thecannawiki/ESP32EnvironmentController/src/globals.cpp

#include "Arduino.h"
#include <EEPROM.h>            // read and write from flash memory
#ifdef HTTP_DELETE
#undef HTTP_DELETE
#endif
// #include <ESPAsyncWebServer.h>
#include "esp_task_wdt.h"      //to feed the task watchdog
#include <vector>
#include <algorithm>
#include "Credentials.h"  
#include <WiFi.h>
#include <WiFiMulti.h>
#include <Wire.h>
#include <SPI.h>
#include <PubSubClient.h>
#include <Adafruit_NeoPixel.h>
#include <ArduinoJson.h>
#include <Preferences.h>
#include <buffer.h>
#include <SensirionI2CScd4x.h>
#include <SparkFunBME280.h> //edit this library to change the i2c address if bme is not found
#include <SparkFun_SGP30_Arduino_Library.h>
#include "globals.h"

SensirionI2CScd4x scd4x;
bool SCD40Mounted = false;
BME280 bme280;
SGP30 sgp30;
bool bmeMounted = false;
bool sgpMounted = false;
Sensor sensorPref = SCD4;


//global vals
//hardware
bool dehumidiferState = false;
bool humidifierState = false;
bool automaticDehumidifier = true;
bool automaticHumidifier = true;
bool automaticFanVpd = true;
bool dehumidifierPrimaryMode = false; // Primary mode means dehumidifier/humidifier will operate on bounds around target humidity. When false (secondary mode) it will control based on fan power usage
bool dehumidifierForTemp = false; // The dehumidifier  will operate on bounds around target temperature. This takes precedence over dehumidifier secondary mode when enabled
int heaterMaxPower = 50;
float heaterPower = heaterMaxPower;
float humidifierPower = 0;
bool heaterTempMode = false;
bool autoHeater = false;
bool pumpState = false;
float fanPower = 30.0f;        //float to 1dp between 0 and 100
float lastPowerVal = 0;        //for fan ramp up control
float minpercentvalue = 0.0f; //min power percentage required to make fan spin e.g 0.25 for 25%
float softMaxFan = 100.0f; //soft upper limit on fan percentage
float softMinFan = 0.0f; //soft lower limit on fan percentage
bool lockHVAC = false;
unsigned long pumpEnd = 0;
unsigned long pumpStart = 0;
unsigned long heaterStart = 0;
unsigned long heaterEnd = 0;
float waterSensor1State = 0;
int w2raw = 0;
float w2mean = 0;

//settings
float targetHumidity = 60;  //Sensible default
float targetVpd = 1.0f;
float targetTemperature = 25.0f;
float ventTemp = 35.0f;
int w1maxWaterSensorVal = 1800;
int w2maxWaterSensorVal = 1800;
bool vpdMode = true;
bool setupMode = false;
char deviceName[40] = "";
char MQTTPUBLISHTOPIC[50] = "";
char MQTTCONTROLTOPIC[50] = "";

//pinout
int dehumidifierControlPin = 34;
int touchWaterSensor = 14;
int humidifierControlPin = 13;
int fanControlPin = 12;
int pumpControlPin = 33;
int waterSensor1Pin= 34;
// int waterSensor2Pin= 4;
int heaterControlPin = 27;
int neopixelPin = 19;
int setupModePin = 23;

//environ vals
float temp = -1;
float humidity = -1;

uint16_t co2 = -1;
float tvoc = 0;
float upperHumidityBound = 60.0f;
float lowerHumidityBound = 40.0f;
char sensorjson[SENSORJSON_SIZE];


Buffer<64> humidityBuffer ;  ///written to every SensorTime
Buffer<64> tempBuffer;
Buffer<64> errorBuffer;
Buffer<64> w1Buffer;
Buffer<128> w2Buffer;
Buffer<500> fanBuffer;   //written to every second
Buffer<500> heaterStateBuffer;   //written to every second
Buffer<300> humidifierStateBuffer;   //written to every second


//PID
float P = 0.1;
float I = 0.1;
float D = 0.1;

//heater PID
float HP = 0.1;
float HD = 0.1;
float HVPDP = 1; // heater vpd (PID) P term
float HVPDD = 1; // heater vpd (PID) D term
float HuVPD_P = 1;
float HuVPD_D = 1;




//time
const char* ntpServer = "pool.ntp.org";
long gmtOffset_sec = 0;
int daylightOffset_sec = 3600;
struct tm timeinfo;
time_t timeNow;

//mqtt
long lastMsg = 0;
char msg[50];
int value = 0;

// setting PWM properties
int freq = 200000;
int heaterFreq = 20000;
int humidifierFreq = 20000;
int fanPWMchannel = 0;
int heaterPWMchannel = 1;
int humidifierPWMchannel = 2;
int resolution = 10;    //10-bit
int maxPWMval = 1023;  // for resolution of 10-bit
bool fanChanged = false;
float fanPowerLimiter = 1.0f; //0-1, limits the fan power to a percentage of the maxPWMval
float heaterSoftMaxPWM = (MAXHEATEROUTPUT / 100.0) * maxPWMval;

//global objects
WiFiMulti wifiMulti;
// AsyncWebServer server(80);
Adafruit_NeoPixel pixels(1, neopixelPin, NEO_GRB + NEO_KHZ800);

TaskHandle_t longPWMTaskHandle = NULL;
TaskHandle_t TransTestTaskHandle = NULL;
TaskHandle_t LedAnimationTaskHandle = NULL;
TaskHandle_t freezewatchdogTaskHandle = NULL;
TaskHandle_t mainLoopTaskHandle = NULL;
TaskHandle_t mqttTaskHandle = NULL;
WiFiClientSecure espClient;
PubSubClient mqttclient(espClient);
Preferences preferences;

//runtime 
int loopCounter = 0;
bool setupReceived = false;
int transTestTime = 0;
time_t humidifierPauseTime = 0;
