thecannawiki/ESP32EnvironmentController/src/globals.h

#include "Arduino.h"
#include <EEPROM.h>            // read and write from flash memory
// #include <ESPAsyncWebServer.h>
#include "esp_task_wdt.h"      //to feed the task watchdog
#include <vector>
#include <algorithm>
#include "Credentials.h"  
#include <WiFi.h>
#include <WiFiMulti.h>
#include <Wire.h>
#include <SPI.h>

#include <PubSubClient.h>
#include <WiFiClientSecure.h>
#include <Adafruit_NeoPixel.h>
#include <ArduinoJson.h>
#include <Preferences.h>
#include "buffer.h"
#include <SensirionI2CScd4x.h>
#include <SparkFunBME280.h> //edit this library to change the i2c address if bme is not found
#include <SparkFun_SGP30_Arduino_Library.h>

#ifndef GLOBALS_H
#define GLOBALS_H

enum Sensor {BM280_SGP30, SCD4};

extern SensirionI2CScd4x scd4x;
extern bool SCD40Mounted;
extern BME280 bme280;
extern SGP30 sgp30;
extern bool bmeMounted;
extern bool sgpMounted;
extern Sensor sensorPref;
//global vals
//hardware


extern bool dehumidiferState;
extern bool humidifierState;
extern bool automaticDehumidifier;
extern bool automaticHumidifier;
extern bool automaticFanVpd;
extern bool dehumidifierPrimaryMode;
extern bool dehumidifierForTemp;
extern int heaterMaxPower;
extern float heaterPower;
extern float humidifierPower;
extern bool heaterTempMode;
extern bool autoHeater;
extern float waterSensor1State;
extern int w2raw;
extern float w2mean;
extern bool pumpState;
extern float fanPower;
extern float lastPowerVal;
extern float softMaxFan;
extern float softMinFan;
extern float minpercentvalue; //min power percentage required to make fan spin 
extern bool lockHVAC;    //prevents changes to any HVAC equiptment

//settings
extern bool vpdMode;
extern bool setupMode;
extern char deviceName[40];
extern char MQTTPUBLISHTOPIC[50];
extern char MQTTCONTROLTOPIC[50];


//pinout
extern int dehumidifierControlPin;
extern int humidifierControlPin;
extern int fanControlPin;
extern int touchWaterSensor;
extern int pumpControlPin;
extern int heaterControlPin;
extern int stirrerControlPin;
extern unsigned long pumpEnd;
extern unsigned long pumpStart;
extern unsigned long heaterStart;
extern unsigned long heaterEnd;
extern int neopixelPin;
extern int waterSensor1Pin;
// extern int waterSensor2Pin;
extern int setupModePin;

//environ vals
extern float temp;
extern float targetHumidity;
extern float targetTemperature;
extern float ventTemp;
extern float humidity;
extern uint16_t co2;
extern float tvoc;
extern float upperHumidityBound;
extern float lowerHumidityBound;
extern float targetVpd;
constexpr size_t SENSORJSON_SIZE = 420; //There is a max size u can send to MQTT broker
extern char sensorjson[SENSORJSON_SIZE];  
extern int w1maxWaterSensorVal;
extern int w2maxWaterSensorVal;

extern Buffer<64> humidityBuffer;
extern Buffer<64> tempBuffer;
extern Buffer<64> errorBuffer;
extern Buffer<64> w1Buffer;
extern Buffer<128> w2Buffer;
extern Buffer<500> fanBuffer;
extern Buffer<500> heaterStateBuffer;
extern Buffer<300> humidifierStateBuffer;


//PID
extern float P;
extern float I;
extern float D;

extern float HP;
extern float HD;

extern float HuVPD_P;
extern float HuVPD_D;

//time
extern const char* ntpServer;
extern long  gmtOffset_sec;
extern int   daylightOffset_sec;
extern struct tm timeinfo;
extern time_t timeNow;

//mqtt
extern long lastMsg;
extern char msg[50];
extern int value;

// setting PWM properties
extern int freq;
extern int heaterFreq;
extern int humidifierFreq;
extern int fanPWMchannel;
extern int heaterPWMchannel;
extern int humidifierPWMchannel;
extern int resolution;
extern int maxPWMval;
extern bool fanChanged;
extern float fanPowerLimiter;
extern float heaterSoftMaxPWM;


//global objects
extern WiFiMulti wifiMulti;
// extern AsyncWebServer server;
extern Adafruit_NeoPixel pixels;

extern TaskHandle_t longPWMTaskHandle;
extern TaskHandle_t LedAnimationTaskHandle;
extern TaskHandle_t TransTestTaskHandle;
extern TaskHandle_t freezewatchdogTaskHandle;
extern TaskHandle_t mainLoopTaskHandle;
extern TaskHandle_t mqttTaskHandle;
extern WiFiClientSecure espClient;
extern PubSubClient mqttclient;
extern Preferences preferences;

//runtime 
extern int loopCounter;
extern bool setupReceived;
extern int transTestTime;
extern time_t humidifierPauseTime;

#endif
