thecannawiki/ESP32EnvironmentController/src/peripherals.h

void pressDehumidifierButton();
void setDehumidifierState(bool state);
void setHumidifierState(bool state);
void setHeaterState(bool state);
void updateHeaterPower();
float PIDDTerm(int lookback_length);
void updateHumidifierPower();
