thecannawiki/ESP32EnvironmentController/src/mathsfunctions.h

float calcTargetHumidityForVpd(float targetVpd, float temp);    //returns the humidity required to hit target VPD at current temp

float calcVpd(float temp, float humidity);

float calcGramsOfWaterInAir(float temp, float humidity);

float calculationAbsHum(float temp, float humidity);
